FunDeckHermit/NURD-Template/NURD-template.kicad_sch

## KiCad design NURD-template.kicad_sch (2026-04-22)

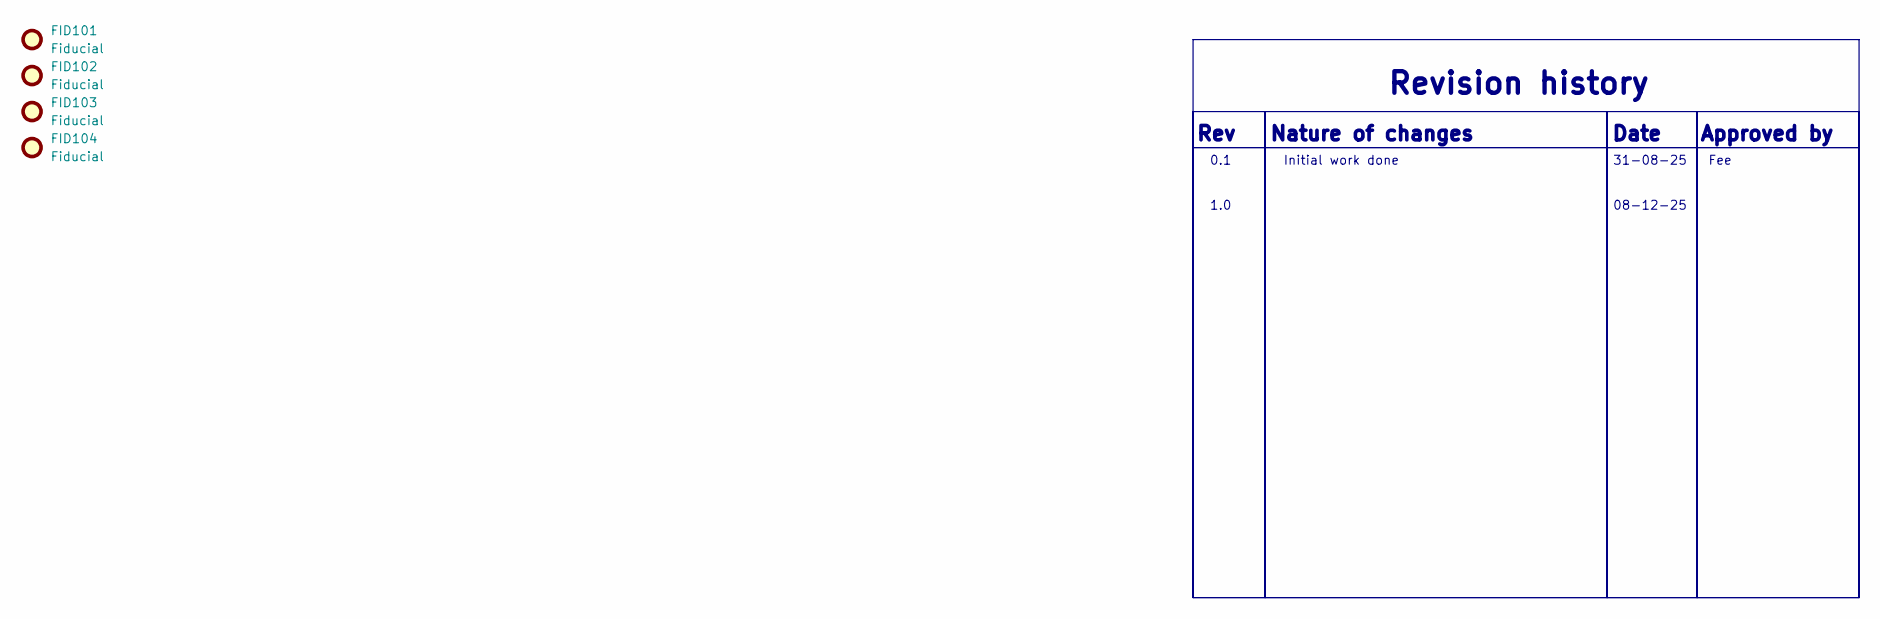
[picture p7: schematic NURD-template.kicad_sch]

Parts:
FID101, FID102, FID103, FID104: Fiducial; Fiducial_0.5mm_Mask1mm

Notes on the sheet:
Nature of changes
Initial work done
1.0
Approved by
Fee
08-12-25
Date
Revision history
0.1
Rev
31-08-25
